cese-dci/tp-SergioAlberino/Poncho_rUVot/Imágenes/3D/Poncho_rUVot.png

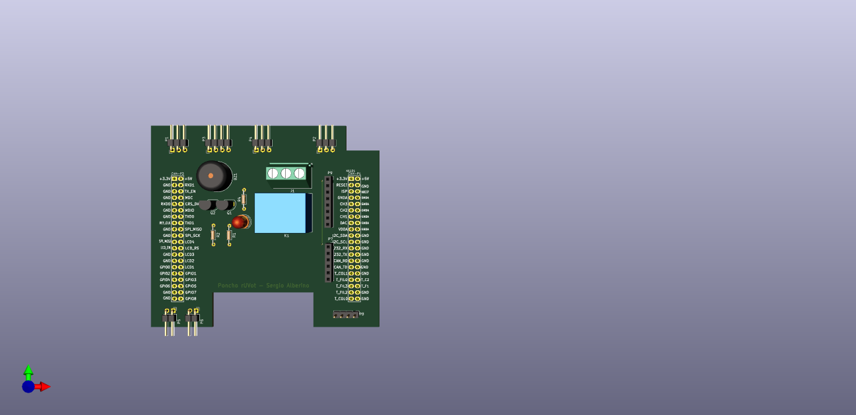
Poncho_rUVot/Imágenes/3D/Poncho_rUVot.png
