cese-dci/tp-SergioAlberino/Poncho_rUVot/Imágenes/3D/Poncho_rUVotvista3.png.png

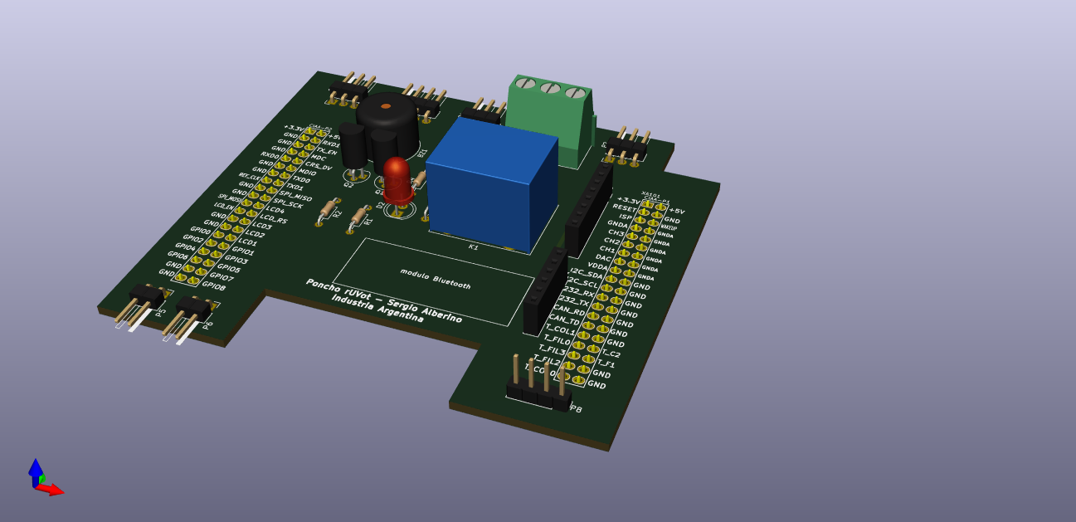
Poncho_rUVot/Imágenes/3D/Poncho_rUVotvista3.png.png
