cese-dci/tp-SergioAlberino/Poncho_rUVot/Imágenes/3D/Poncho_rUVotvista33.png

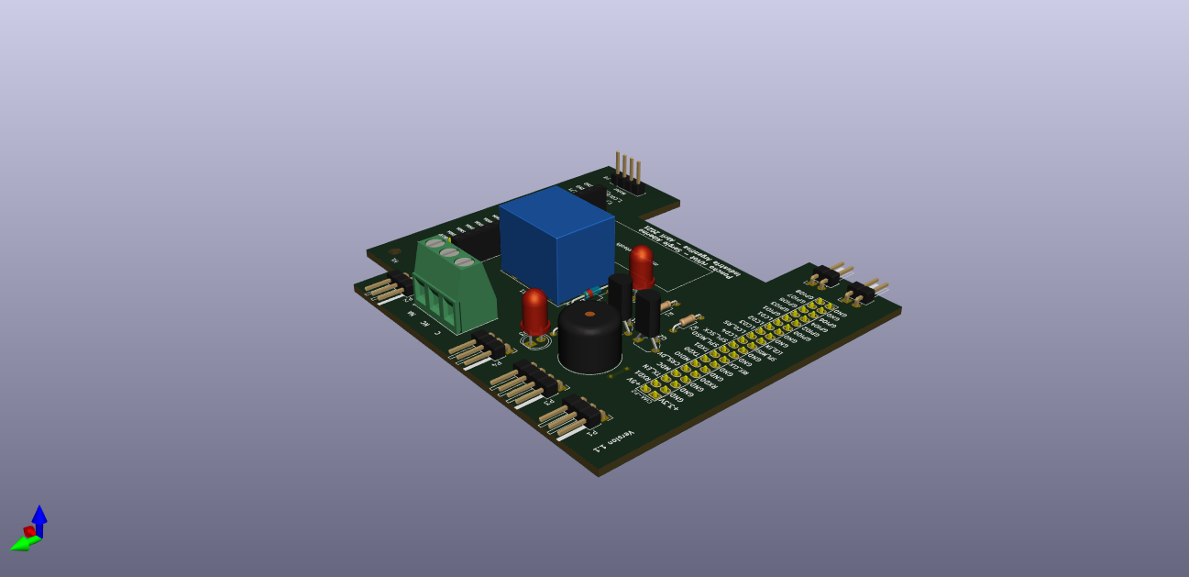
Poncho_rUVot/Imágenes/3D/Poncho_rUVotvista33.png
