cese-dci/tp-SergioAlberino/Poncho_rUVot/Imágenes/3D/Poncho_rUVotvista.png

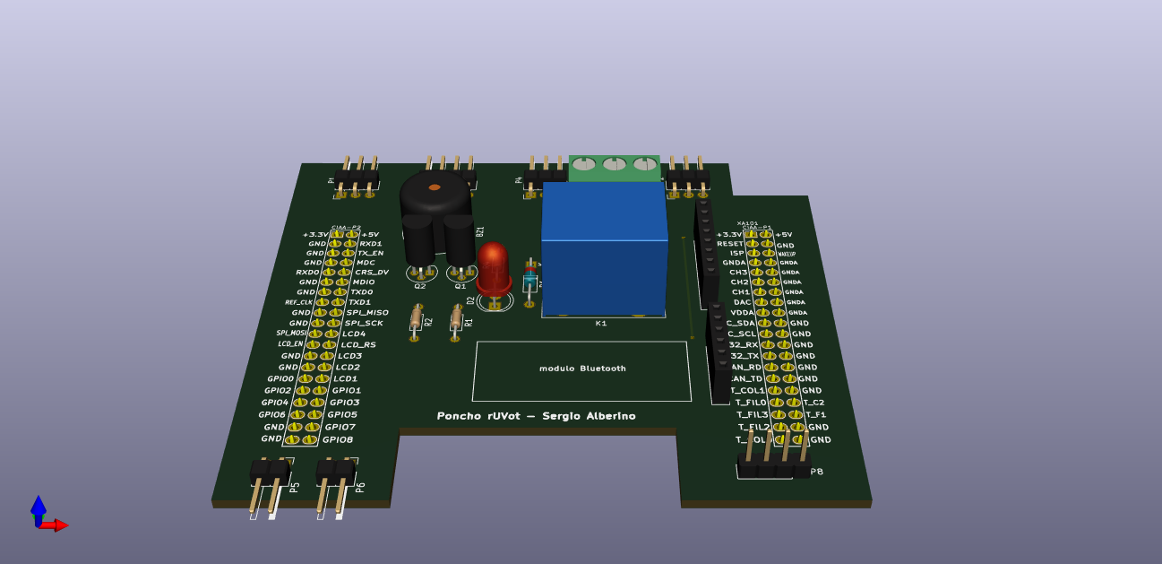
Poncho_rUVot/Imágenes/3D/Poncho_rUVotvista.png
