cese-dci/tp-SergioAlberino/Poncho_rUVot/Imágenes/3D/primeravista3d.png

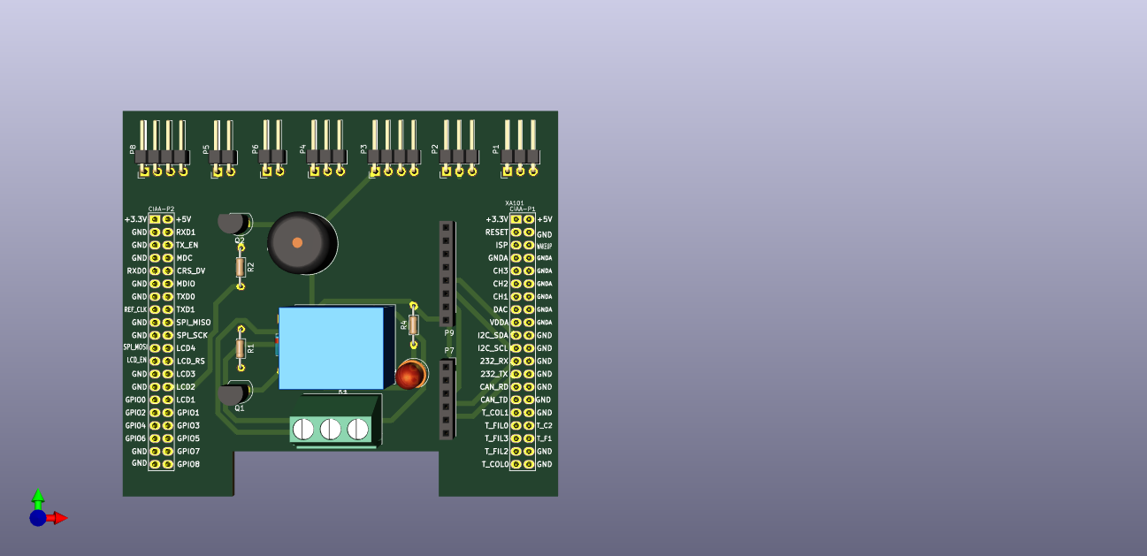
Poncho_rUVot/Imágenes/3D/primeravista3d.png
