cese-dci/tp-SergioAlberino/Poncho_rUVot/Imágenes/Fotos/IMG_20210517_114525.jpg

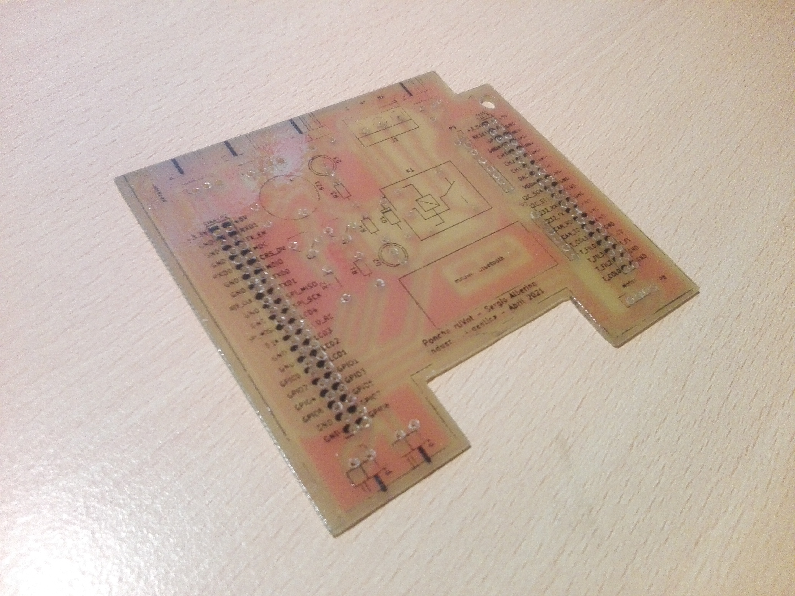
Poncho_rUVot/Imágenes/Fotos/IMG_20210517_114525.jpg
