cese-dci/tp-SergioAlberino/Poncho_rUVot/Imágenes/Fotos/IMG_20210517_140837.jpg

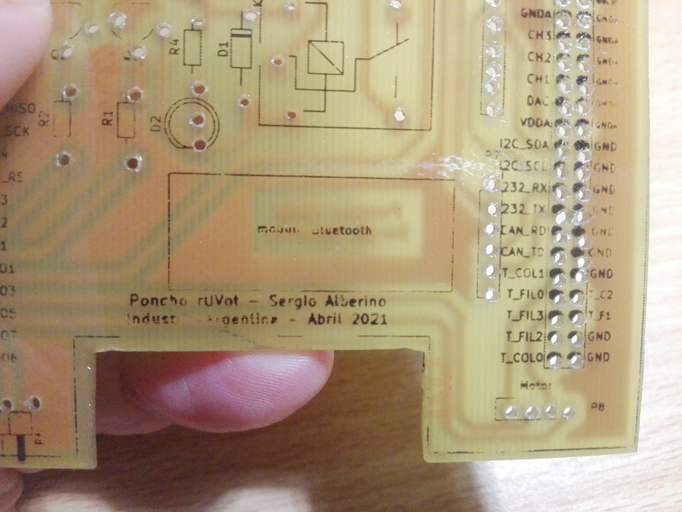
Poncho_rUVot/Imágenes/Fotos/IMG_20210517_140837.jpg
