cese-dci/tp-SergioAlberino/Poncho_rUVot/Imágenes/Fotos/Proceso/IMG_20210514_113516.jpg

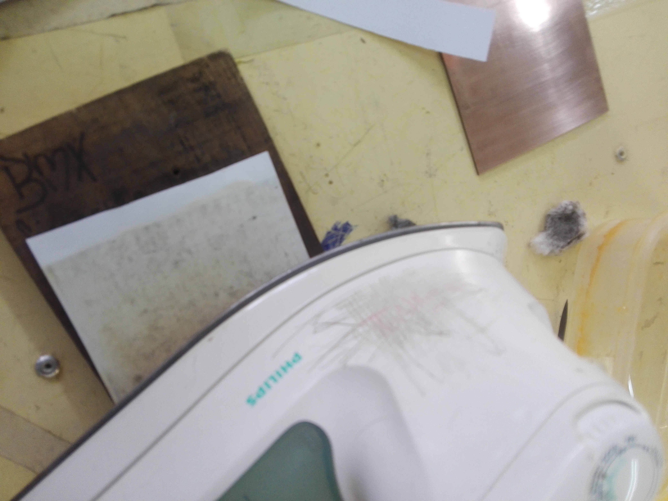
Poncho_rUVot/Imágenes/Fotos/Proceso/IMG_20210514_113516.jpg
