cese-dci/tp-SergioAlberino/Poncho_rUVot/Imágenes/Fotos/Proceso/IMG_20210514_113517.jpg

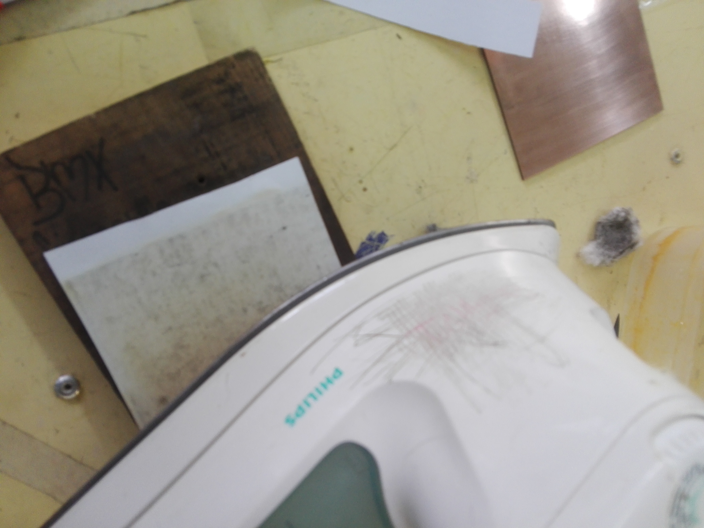
Poncho_rUVot/Imágenes/Fotos/Proceso/IMG_20210514_113517.jpg
