cese-dci/tp-SergioAlberino/Poncho_rUVot/Imágenes/Fotos/Proceso/IMG_20210514_120109.jpg

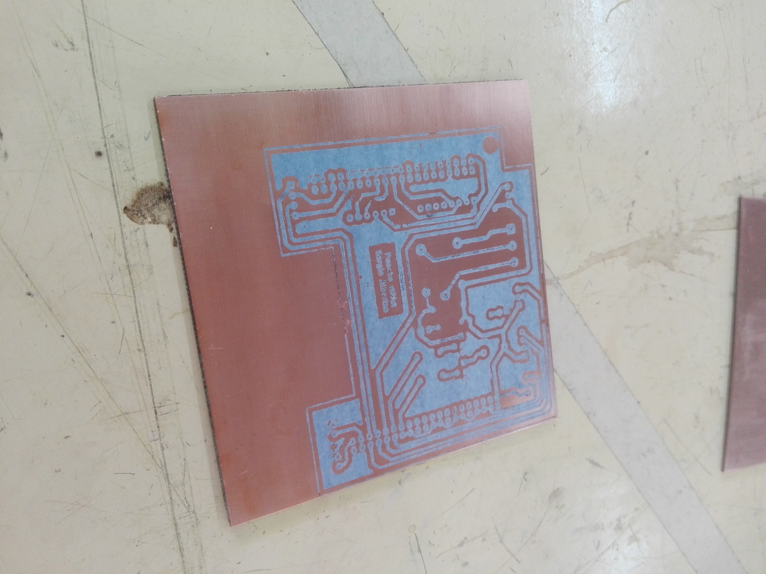
Poncho_rUVot/Imágenes/Fotos/Proceso/IMG_20210514_120109.jpg
