cese-dci/tp-SergioAlberino/Poncho_rUVot/Imágenes/Fotos/Proceso/IMG_20210514_120120.jpg

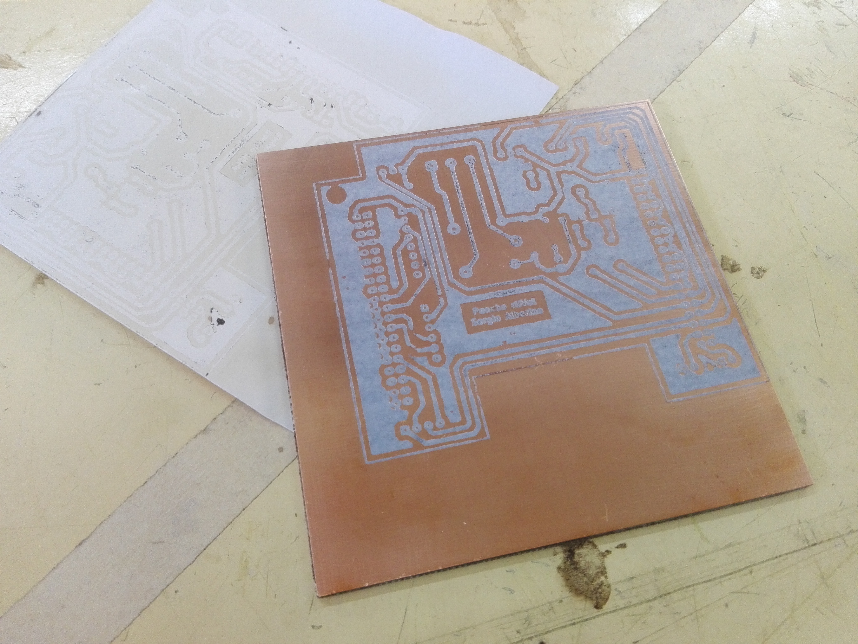
Poncho_rUVot/Imágenes/Fotos/Proceso/IMG_20210514_120120.jpg
