cese-dci/tp-SergioAlberino/Poncho_rUVot/Imágenes/Fotos/Proceso/IMG_20210515_172034.jpg

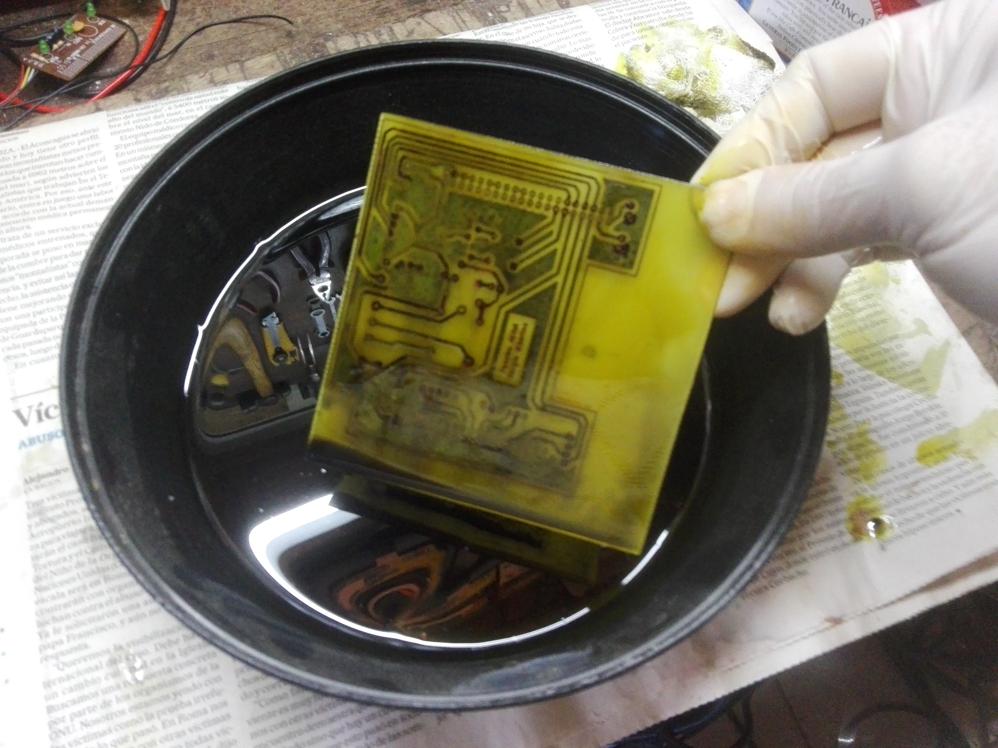
Poncho_rUVot/Imágenes/Fotos/Proceso/IMG_20210515_172034.jpg
