cese-dci/tp-SergioAlberino/Poncho_rUVot/Imágenes/Fotos/Proceso/IMG_20210515_173354.jpg

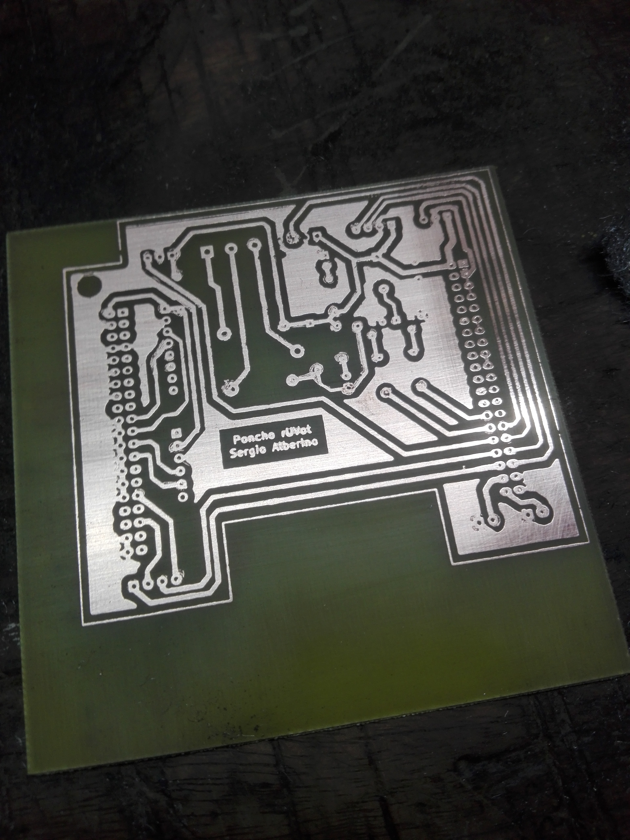
Poncho_rUVot/Imágenes/Fotos/Proceso/IMG_20210515_173354.jpg
