cese-dci/tp-SergioAlberino/Poncho_rUVot/Imágenes/Fotos/Proceso/IMG_20210515_210557.jpg

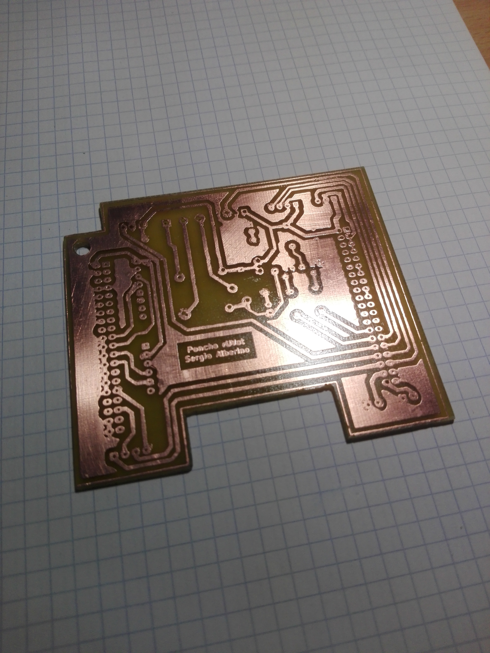
Poncho_rUVot/Imágenes/Fotos/Proceso/IMG_20210515_210557.jpg
